thinklearndo/keychain_backup_pi/filesystem/usr/share/keychain_manager/backup_running.jpg

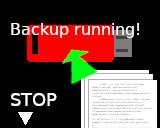
filesystem/usr/share/keychain_manager/backup_running.jpg
