thinklearndo/keychain_backup_pi/filesystem/usr/share/keychain_manager/no_usb_idle.jpg

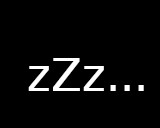
filesystem/usr/share/keychain_manager/no_usb_idle.jpg
