thinklearndo/keychain_backup_pi/filesystem/usr/share/keychain_manager/safe_to_remove_no_space.jpg

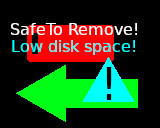
filesystem/usr/share/keychain_manager/safe_to_remove_no_space.jpg
