thinklearndo/keychain_backup_pi/filesystem/usr/share/keychain_manager/usb.jpg

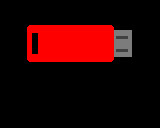
filesystem/usr/share/keychain_manager/usb.jpg
