thinklearndo/keychain_backup_pi/filesystem/usr/share/keychain_manager/usb_bad.jpg

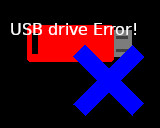
filesystem/usr/share/keychain_manager/usb_bad.jpg
