thinklearndo/keychain_backup_pi/filesystem/usr/share/keychain_manager/usb_good_no_space.jpg

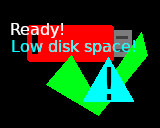
filesystem/usr/share/keychain_manager/usb_good_no_space.jpg
