thinklearndo/keychain_backup_pi/filesystem/usr/share/keychain_manager/usb_idle.jpg

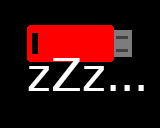
filesystem/usr/share/keychain_manager/usb_idle.jpg
