thinklearndo/keychain_backup_pi/filesystem/usr/share/keychain_manager/usb_no_space.png

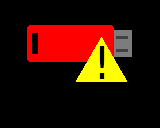
filesystem/usr/share/keychain_manager/usb_no_space.png
