thinklearndo/keychain_backup_pi/filesystem/usr/share/keychain_manager/usb_wait.jpg

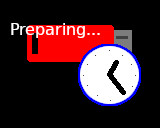
filesystem/usr/share/keychain_manager/usb_wait.jpg
