thinklearndo/keychain_backup_pi/filesystem/usr/share/keychain_manager/wifi_good.jpg

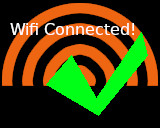
filesystem/usr/share/keychain_manager/wifi_good.jpg
