thinklearndo/keychain_backup_pi/filesystem/usr/share/keychain_manager/wifi_wait.jpg

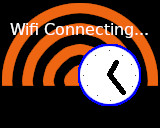
filesystem/usr/share/keychain_manager/wifi_wait.jpg
